BASM/MAX-UART/max232.sch

## KiCad design max232.sch (2013-09-20, an earlier design)

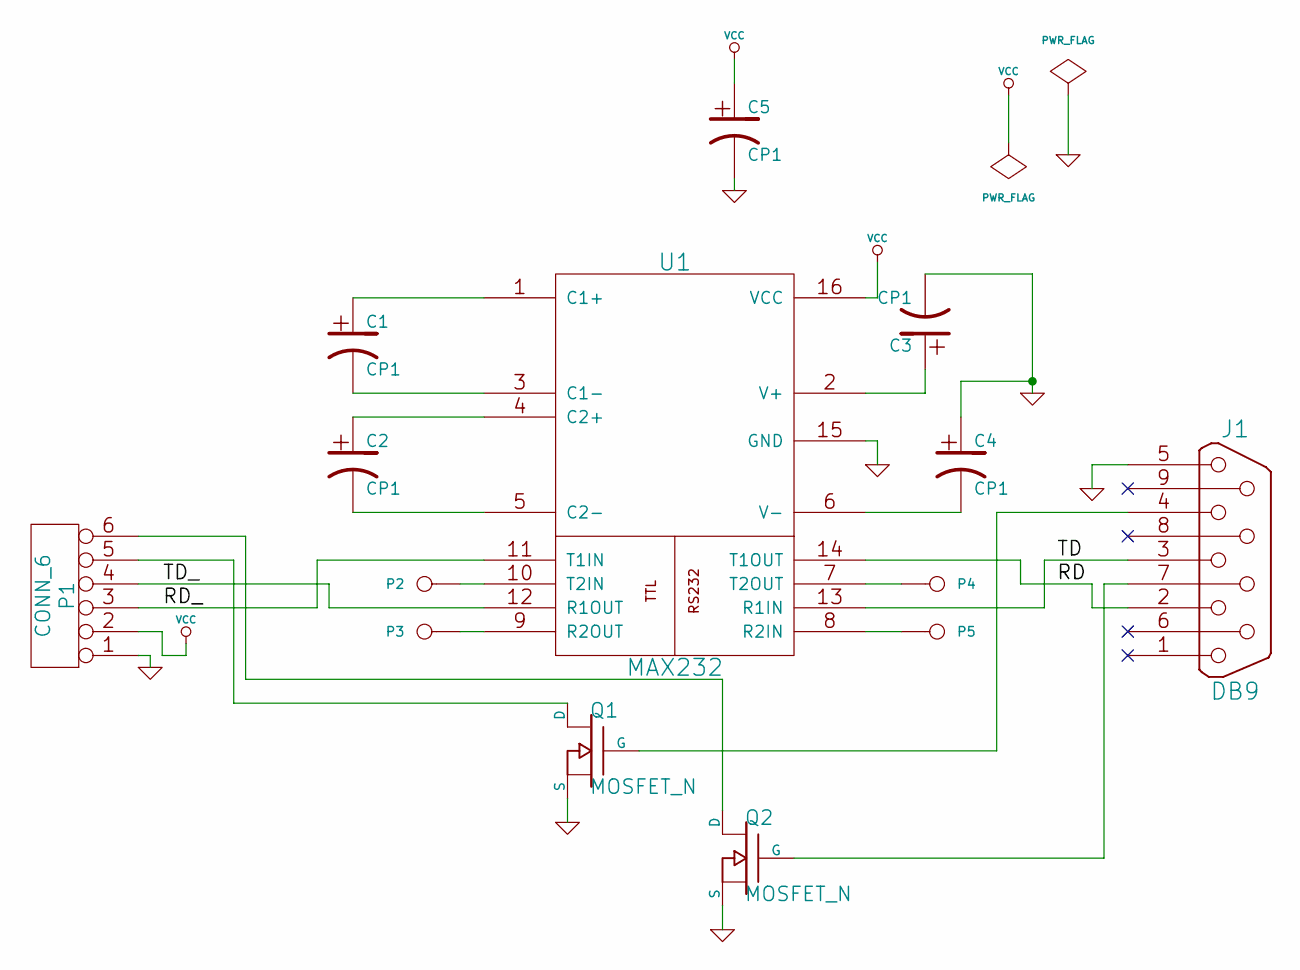
[picture p3: schematic max232.sch]

Parts:
C1, C2, C3, C4, C5: CP1
J1: DB9
P1: CONN_6
P2, P3, P4, P5: CONN_1
Q1, Q2: MOSFET_N
U1: MAX232

Connections:
GND: C3.2, C4.1, C5.2, J1.5, P1.1, Q1.S, Q2.S, U1.15 (GND)
unnamed: C1.1, U1.1 (C1+)
unnamed: C1.2, U1.3 (C1-)
unnamed: C2.1, U1.4 (C2+)
unnamed: C2.2, U1.5 (C2-)
unnamed: C3.1, U1.2 (V+)
unnamed: C4.2, U1.6 (V-)
unnamed: J1.4, Q1.G
unnamed: J1.7, Q2.G
unnamed: P1.5, Q1.D
unnamed: P1.6, Q2.D
unnamed: P2.1, U1.10 (T2IN)
unnamed: P3.1, U1.9 (R2OUT)
unnamed: P4.1, U1.7 (T2OUT)
unnamed: P5.1, U1.8 (R2IN)
RD: J1.2, U1.14 (T1OUT)
RD_: P1.3, U1.11 (T1IN)
TD: J1.3, U1.13 (R1IN)
TD_: P1.4, U1.12 (R1OUT)
VCC: C5.1, P1.2, U1.16 (VCC)
